klushok-etv/schrodingers-lantern/image/20210728_142154.jpg

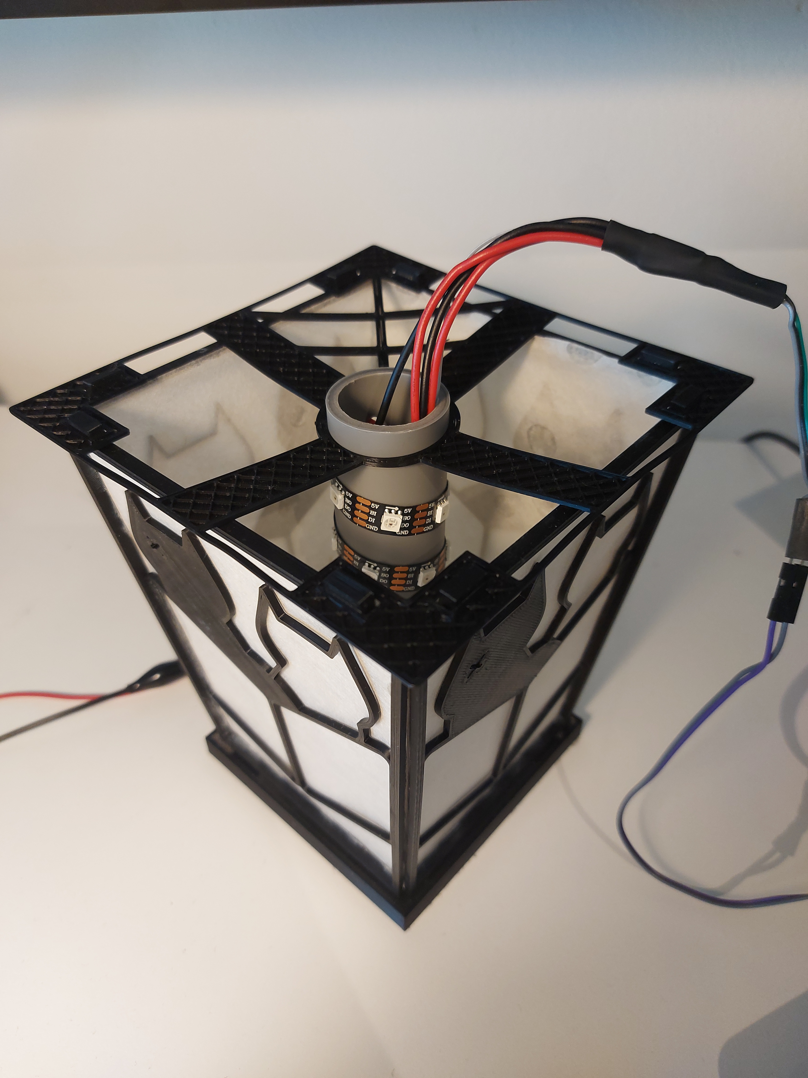
image/20210728_142154.jpg
