klushok-etv/schrodingers-lantern/image/assembly.png

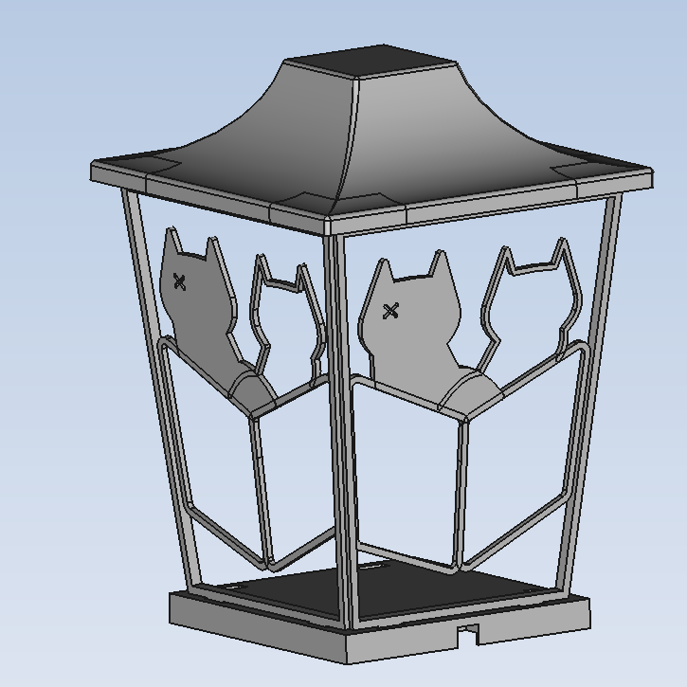
image/assembly.png
