klushok-etv/schrodingers-lantern/firmware/server/src/Effect.cpp

#include "Effect.h"

Effect::Effect(CRGB *leds, uint32_t delay)
{
    this->_leds = leds;
    this->_delay = delay;
}

void Effect::fillSolid(CRGB color)
{
    for (uint8_t i = 0; i < NUM_LEDS; i++)
    {
        this->_leds[i] = color;
    }
    FastLED.show();
}

void Effect::run()
{
    // only execute if specified delay has elapsed
    if (millis() - this->_prev_t < this->_delay)
        return;
    this->_prev_t = millis();

    this->effectStep();
}

void Effect::setColors(CRGB *, uint8_t)
{
    Serial.println("WARNING - setColors() must be implemented by derived effect classes!");
}

void Effect::setColorPalette(CRGBPalette16 )
{
    Serial.println("WARNING - setColorPalette() must be implemented by derived effect classes!");
}

void Effect::setDelay(uint32_t delay){
    this->_delay = delay;
}

void Effect::setFPS(uint32_t fps){
    this->setDelay(1000/fps);
}
