klushok-etv/schrodingers-lantern/firmware/server/src/Flame.h

#ifndef FLAME_H
#define FLAME_H

#include "Effect.h"

class Flame : public Effect
{
private:
    const uint8_t _layer_size = 6;
    uint8_t _cooling;
    uint8_t _sparking;
    CRGBPalette16 _gPal;
    byte heat[NUM_LEDS];

public:
    Flame(CRGB*, uint32_t, uint8_t, uint8_t);
    ~Flame(){};
    void effectStep();
    void setColorPalette(CRGBPalette16);
};

#endif
