klushok-etv/schrodingers-lantern/image/20210707_221820.jpg

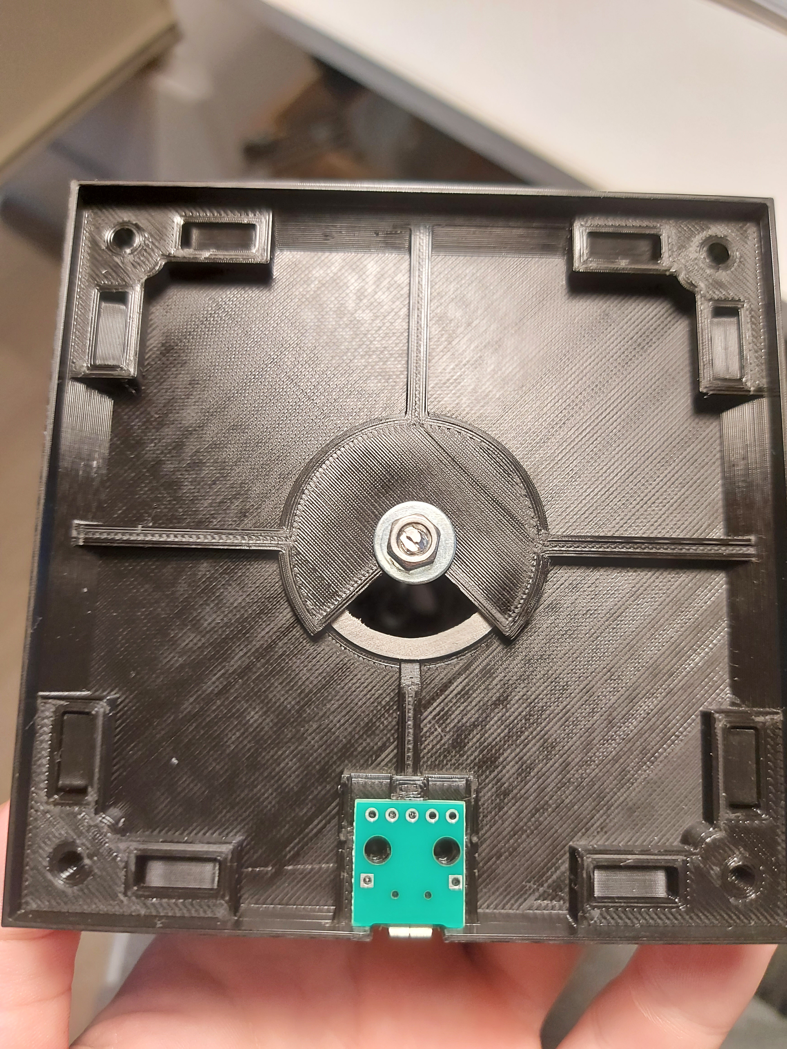
image/20210707_221820.jpg
